shohei/solenoid_control/ltspice/2n7002.asc

D1: diode
L1: ind; 33m
M1: nmos; 2N7002
R1: res; 100
R2: res; 10k
R3: res; 33; tol=1 pwr=0.1
V1: voltage; 12
V2: voltage; PULSE(0 5 0 .001u .001u 12.6m 20m 50)
Named nets: 0, Vin, Vd, V1
.tran 60m
