shohei/solenoid_control/ltspice/bjt.asc

D1: diode
L1: ind; 55m
Q1: npn; MyBJT
R1: res; 33
R2: res; 5k
R3: res; 10
V1: voltage; PULSE(0 5 .5 .01u .01 1)
V2: voltage; 12
Named nets: 0
.tran 1
.step param MyBF list 50 100 200
.MODEL MyBJT AKO: 2N2222 (Bf=MyBF)
