shohei/solenoid_control/ltspice/bs170.asc

R1: res; 100
R2: res; 10k
U1: BS_MMBF170
V1: voltage; PULSE(0 2.1 .5 .1 0 1)
V2: voltage; 12
Named nets: 0, SIGNAL, D, S
.tran 1
