shohei/solenoid_control/ltspice/lpf.asc

C1: cap; 0.022µ; V=50 Irms=0 Rser=0 Lser=0 mfg="Murata" pn="GCM155R71H223KA55" type="X7R"
C2: cap; 0.01µ; V=50 Irms=0 Rser=0 Lser=0 mfg="Murata" pn="GCM155R71H103KA55" type="X7R"
R1: res; 10K; tol=1 pwr=0.1
R2: res; 10K; tol=1 pwr=0.1
U1: LT1115
V1: signal; SINE(0 2 500)
V2: cell; 12
V3: cell; -12
Named nets: 0, Vin, OUTPUT, Vcc, Vee
2nd active low pass filter
.tran 10m
.meas TRAN Tcyc TRIG V(Vin)=0V TD=1.8m RISE=1 TARG V(Vin)=0V TD=1.8m RISE=2
.meas TRAN Freq PARAM 1/Tcyc
.meas TRAN Vin(ave) AVG V(Vin) From 1.8ms TO 5.4ms
.meas TRAN Vin(rms) RMS V(Vin) FROM 1.8ms TO 5.4ms
