shohei/solenoid_control/ltspice/simulation1_only_R.asc

Q1: npn
R1: res; 121; tol=1 pwr=0.1
V2: cell; PULSE(0 5 5m 1m 1m 10m)
V3: cell; 12
Named nets: 0
.tran 10m
